Cerberus74/RotorHazard/src/node/readme_S32_BPill.md

# S32_BPill Nodes

*Note:* The recommended method for installing the currently-released node firmware onto the S32_BPill processor is to use the `Update Nodes` button (in the 'System' section on the 'Settings' page) on the RotorHazard web GUI. The steps described below are for developers who wish to build the node firmware from the source code.

## Compiling and Uploading with the Arduino IDE

The node code may be loaded (or flashed) onto the S32_BPill processor by loading the code into the Arduino IDE program and using its 'Upload' function. Arduino IDE version 1.8 or newer is required, and it can be downloaded from https://www.arduino.cc/en/Main/Software

Support for STM32 processors in the Arduino IDE is provided by the [STM32duino project](https://github.com/stm32duino). The installation steps are described in detail on the STM32duino "[Getting Started](https://github.com/stm32duino/wiki/wiki/Getting-Started)" page. The basic steps are as follows:

1. In the "Preferences" dialog add the following link to the "Additional Boards Managers URLs" field:

`https://github.com/stm32duino/BoardManagerFiles/raw/master/STM32/package_stm_index.json`

2. In the "Tools" menu, select "Board" | "Boards Manager"; select "Contributed" type; select "STM32 Cores", select a version and click on install. (The newest version is usually the one you want.) After the installation is complete you can close the Board Manager.

3. In the "Tools" menu, select "Board" | "Boards Manager..." | "STM32 Boards (selected from submenu)" | "Generic STM32F1 Series"

4. In the "Tools" menu, select "Board part number" | "BluePill F103C8"

5. In the "Tools" menu the Serial, USB, and library items my be left at their default values; this is a typical setup:
```
  Board:  "Generic STM32F1 series"
  Board part number:  "BluePill F103C8"
  U(S)ART support:  "Enabled (generic 'Serial')"
  USB support (if available):  "None"
  USB speed (if available):  "Low/Full Speed"
  Optimize:  "Smallest (-Os default)"
  C Runtime Library:  "Newlib Nano (default)"
```

6. In the Arduino IDE, select "File | Open" and navigate to where the `src/node` directory is located, and click on the "node.ino" file to open the node-code project.

7. Click on the 'Verify' button to confirm that the code can be built successfully.

8. The code may be uploaded to the processor on the RotorHazard S32_BPill board by connecting an FTDI to the 6-pin J4 ("BPill Serial FTDI Link") connector on the board. (The other end of the FTDI is connected to the USB port on a PC.) The Raspberry Pi must not be powered on during programming. In the Arduino IDE the serial port (under "Tools | Port") will need to be set to match the connected FTDI.  (If you view the "Tools | Port" selections before and after connecting the FTDI, you should see its serial-port name appear.) In the "Tools" menu, set the "Upload method" to "STM32CubeProgrammer (Serial)". Clicking on the 'Upload' button should flash the code onto the S32_BPill processor.

## Command-line Compiling and Uploading (S32_BPill Nodes)

Command-line batch/script files for compiling and uploading the node code may be found in the `src/node/scripts` directory. For these files to work, the Arduino IDE needs to be installed -- Arduino IDE version 1.8 or newer is required, and it can be downloaded from https://www.arduino.cc/en/Main/Software

The following batch/script files are available:

* *install_stm32_boards* : Installs the required support libraries into the Arduino IDE installation. This can take a few minutes, but only needs to be run once to install the libraries

* *build_stm32* : Builds the S32_BPill node code (for the STM32F103C8 module), creating the firmware file `src/node/build_stm32/RH_S32_BPill_node.bin`

* *build_stm32_f4* : Builds the S32_BPill node code (for the STM32F411CE "[Black Pill](https://github.com/WeActTC/MiniSTM32F4x1)" module), creating the firmware file `src/node/build_stm32/RH_S32_BPill_node_F4.bin`

* *upload_stm32* : Builds the S32_BPill node code and uploads it using the serial (COM) port specified as the first argument. An optional second argument, "--skipBuild", may be specified to skip the build and upload the last firmware file that was built. See the last step [above](#s32ftdi) for info on using an FTDI for uploading

* *upload_stm32_F4* : Version of 'upload_stm32' for the STM32F411CE "[Black Pill](https://github.com/WeActTC/MiniSTM32F4x1)" module

## Compiling and Uploading with Sloeber Eclipse (S32_BPill Nodes)

The node code may also be edited and built using the [Sloeber-Eclipse IDE](http://eclipse.baeyens.it). To install Sloeber-Eclipse:

1. Install Sloeber-Eclipse (V4.3.3 or later) from http://eclipse.baeyens.it <br>
  Note: The length of install path should be less than 26 characters ([Sloeber limitation](https://github.com/Sloeber/arduino-eclipse-plugin/issues/705))

2. Install STM32 Cores into Sloeber-Eclipse:
  * Open "Arduino > Preferences"
  * In the tree view that pops up, go to "Arduino > Third party index url's" and add the STM32 support package URL:

`https://raw.githubusercontent.com/stm32duino/BoardManagerFiles/master/STM32/package_stm_index.json`

3. In "Arduino | Preferences | Platforms and Boards" select 'STM32 Core' version 1.7.0 <br>
  Note:  There are newer version availble, but it seems like if version >= 1.8.0 is used then the builds fail

S32_BPill-node project files for Sloeber-Eclipse may be found in the `src/node/project_files/eclipse_sloeber` directory -- copy these files to the `src/node` directory. Then, in Sloeber-Eclipse, the node-code project may be loaded via "File | Open Projects from File System..."

In "Project" | "Properties" | "Arduino" the "Arduino board selection" settings should be similar to these:
```
Platform folder:  .../STM32/hardware/stm32/1.7.0
Board:  Generic STM32F1 series
Upload Protocol:  Default
Port:  [COM for FTDI]
Optimize:  Smallest (-Os default)
Board part number:  BluePill F103C8
C Runtime Library:  Newlib Nano (default)
Upload method:  STM32CubeProgrammer (Serial)
USB support:  None
U(S)ART support:  Enabled (generic 'Serial')
USB speed:  Low/Full Speed
```

Hitting the 'Verify' button will build the code, which should create the firmware file `src/node/Release/rhnode_S32_BPill.bin`
