Cerberus74/RotorHazard/resources/PCB/RH_PCB_1_2_dimensions.jpg

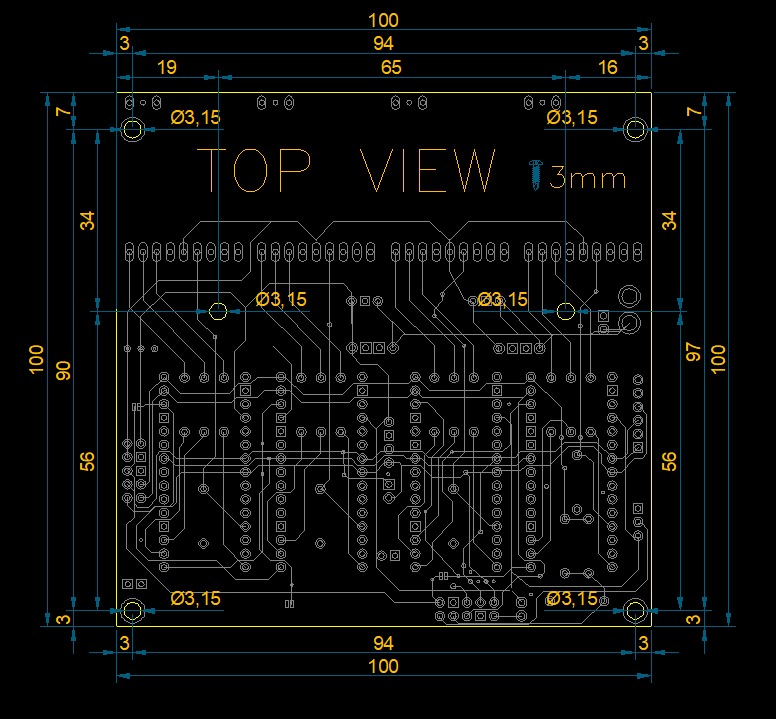
resources/PCB/RH_PCB_1_2_dimensions.jpg
