Cerberus74/RotorHazard/resources/S32_BPill_PCB/pic/RH_S32_BPill_Boot0Jumper.jpg

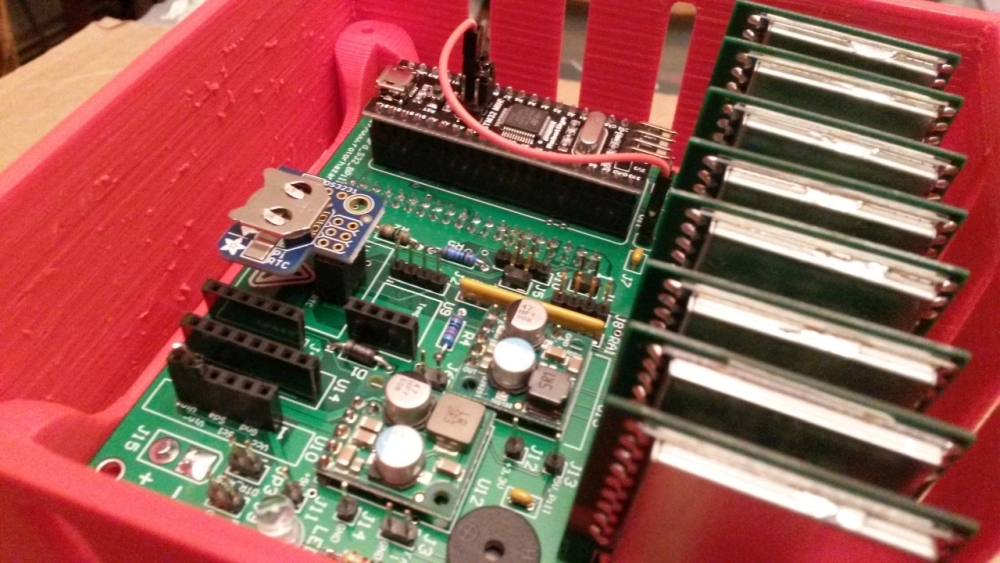
resources/S32_BPill_PCB/pic/RH_S32_BPill_Boot0Jumper.jpg
