Cerberus74/RotorHazard/resources/enclosure/Grille RotorHazard.stl

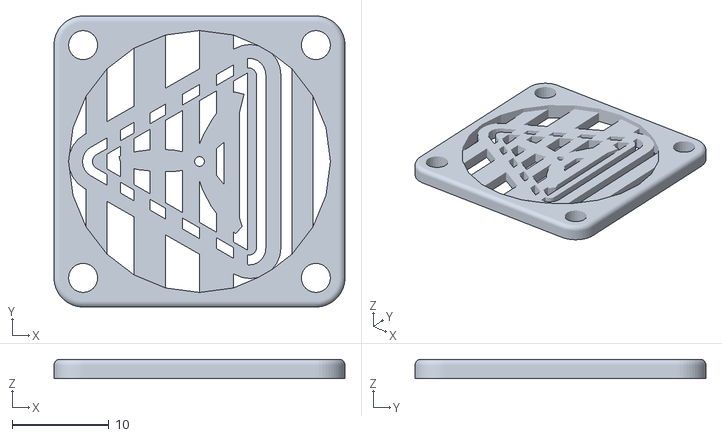
[picture p42: CAD file, 2020-08-13]
resources/enclosure/Grille RotorHazard.stl
30.0 x 30.0 x 2.00
