Cerberus74/RotorHazard/resources/enclosure/Box Four Node.stl

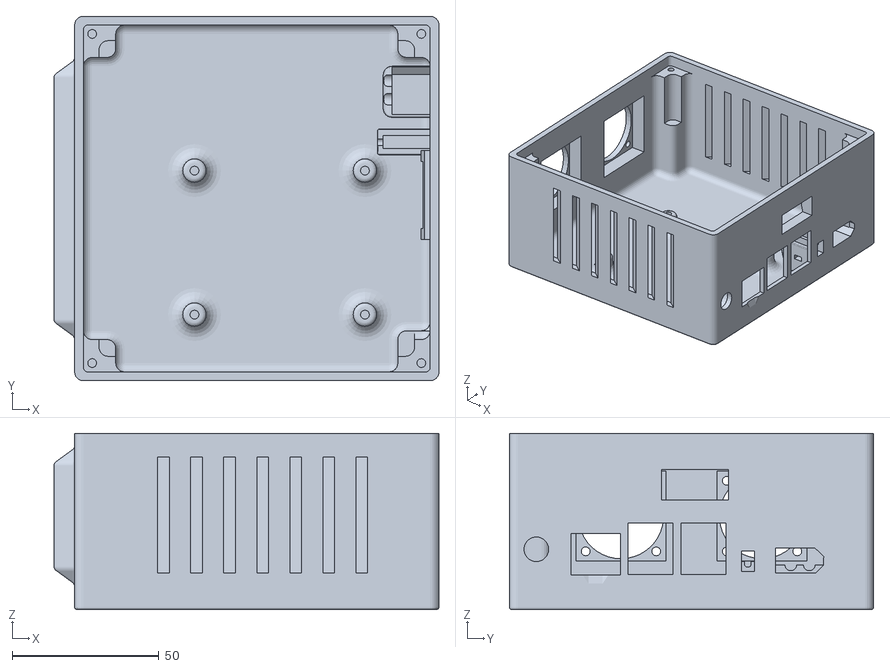
[picture p43: CAD file, 2020-08-13]
resources/enclosure/Box Four Node.stl
131.0 x 124.0 x 59.9
