Cerberus74/RotorHazard/src/node/node.ino

//This '.ino' file is a stub to support building via the original
// Arduino IDE.  The real code is in the '.cpp' and '.h' files.
//
//The NODE_NUMBER definition is now in the 'config.h' file.
//
//The project may be edited and built using Eclipse and the
// "Eclipse C++ IDE for Arduino" plugin:
// https://marketplace.eclipse.org/content/eclipse-c-ide-arduino
