Cerberus74/RotorHazard/src/server/data_export_csv.py

'''CSV data exporter'''

import logging
logger = logging.getLogger(__name__)
import RHUtils
import io
import csv
from data_export import DataExporter

def write_csv(data):
    output = io.StringIO()
    writer = csv.writer(output, quoting=csv.QUOTE_NONNUMERIC)
    writer.writerows(data)

    return {
        'data': output.getvalue(),
        'encoding': 'text/csv',
        'ext': 'csv'
    }

def assemble_all(RHData, PageCache, Language):
    payload = {}
    payload['Pilots'] = assemble_pilots(RHData, PageCache, Language)
    payload['Heats'] = assemble_heats(RHData, PageCache, Language)
    payload['Classes'] = assemble_classes(RHData, PageCache, Language)
    payload['Formats'] = assemble_formats(RHData, PageCache, Language)
    payload['Results'] = assemble_results(RHData, PageCache, Language)

    output = []
    for datatype in payload:
        output.append([datatype])
        for data in payload[datatype]:
            output.append(data)
        output.append('')

    return output

def assemble_pilots(RHData, PageCache, Language):
    payload = [[Language.__('Callsign'), Language.__('Name'), Language.__('Team')]]

    pilots = RHData.get_pilots()
    for pilot in pilots:
        payload.append([pilot.callsign, pilot.name, pilot.team])

    return payload

def assemble_heats(RHData, PageCache, Language):
    payload = [[Language.__('Name'), Language.__('Class'), Language.__('Pilots')]]
    for heat in RHData.get_heats():
        note = heat.note

        if heat.class_id != RHUtils.CLASS_ID_NONE:
            race_class = RHData.get_raceClass(heat.class_id).name
        else:
            race_class = None

        row = [note, race_class]

        heatnodes = RHData.get_heatNodes_by_heat(heat.id)
        for heatnode in heatnodes:
            if heatnode.pilot_id != RHUtils.PILOT_ID_NONE:
                row.append(RHData.get_pilot(heatnode.pilot_id).callsign)
            else:
                row.append('-')

        payload.append(row)

    return payload
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
